TheLittleEngineers/CC3-MPI-26-3124-Satellite-Board/Board Outline-6c00e133356300f3b6208f0038f61ca9.png

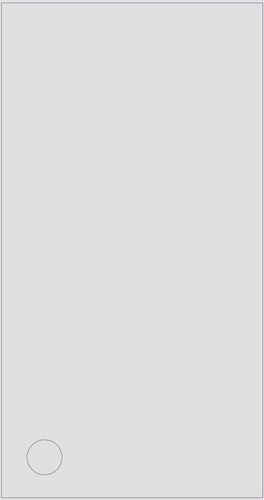
Board Outline-6c00e133356300f3b6208f0038f61ca9.png
