TheLittleEngineers/CC3-MPI-26-3124-Satellite-Board/Board Top-3c8a1014af92d2da4d485e0c789fc6d5.png

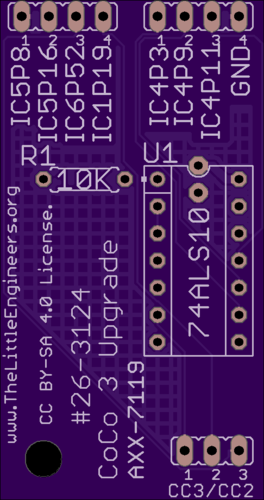
Board Top-3c8a1014af92d2da4d485e0c789fc6d5.png
