TheLittleEngineers/CC3-MPI-26-3124-Satellite-Board/Drills-a1b097b467ef15119a529217e354051c.png

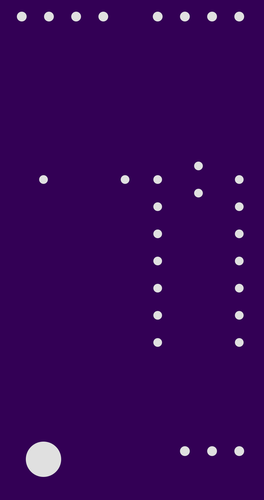
Drills-a1b097b467ef15119a529217e354051c.png
