TheLittleEngineers/CC3-MPI-26-3124-Satellite-Board/Bottom Solder Mask-2cf21228b0f1d5d6e76fb808de184a02.png

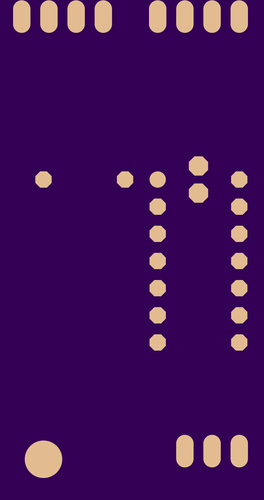
Bottom Solder Mask-2cf21228b0f1d5d6e76fb808de184a02.png
